iostwestcoast/Locker/Photos/photo_2022-11-24_02-31-49.jpg

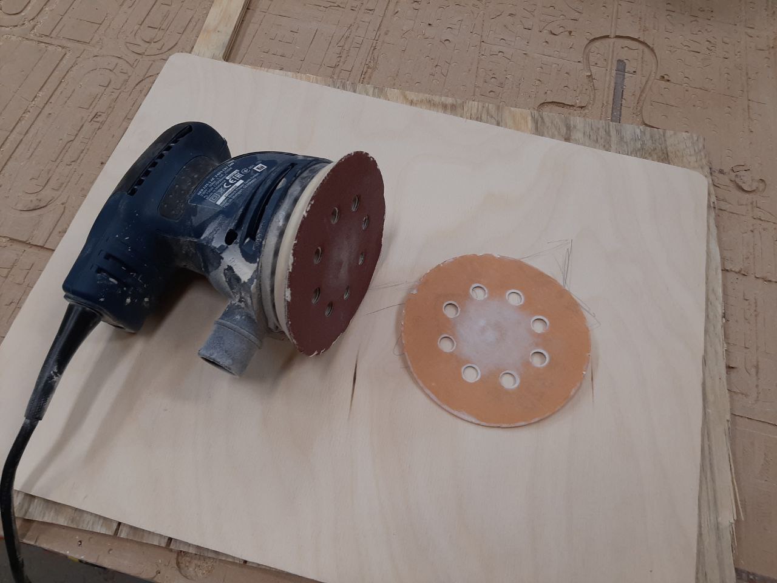
Photos/photo_2022-11-24_02-31-49.jpg
