iostwestcoast/Locker/Photos/photo_2022-11-24_02-31-54.jpg

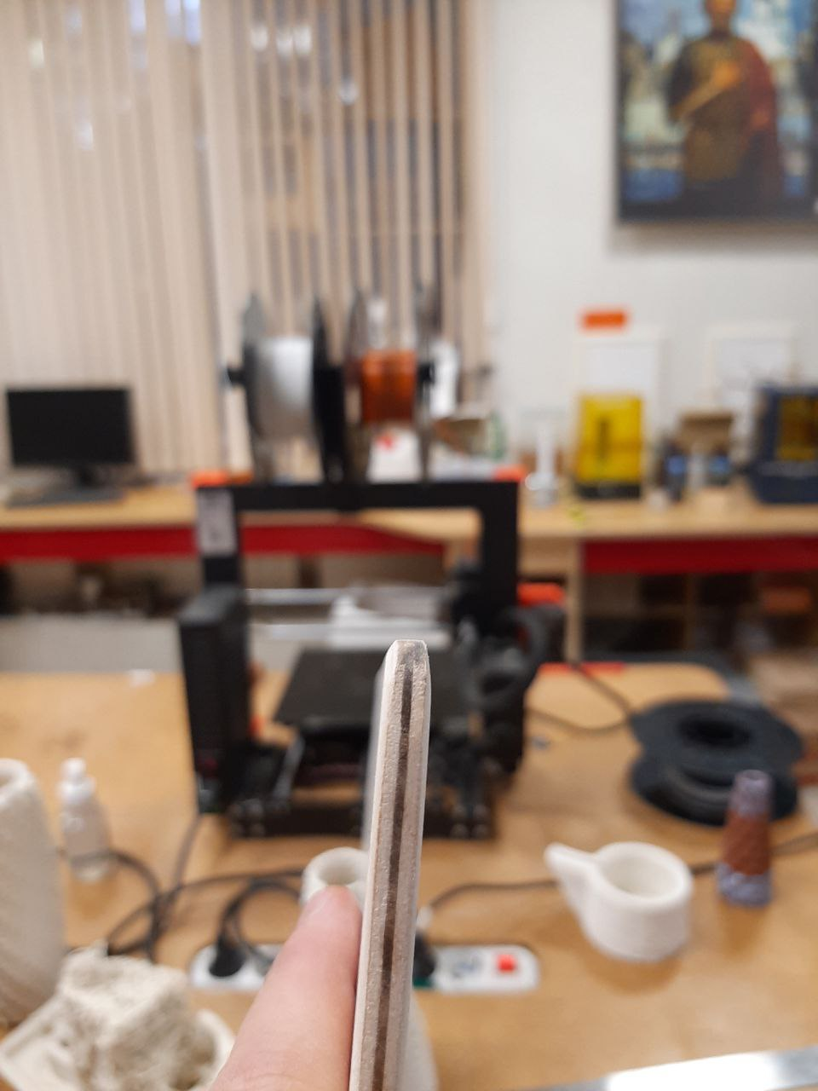
Photos/photo_2022-11-24_02-31-54.jpg
