iostwestcoast/Locker/Photos/photo_2022-11-24_02-32-23.jpg

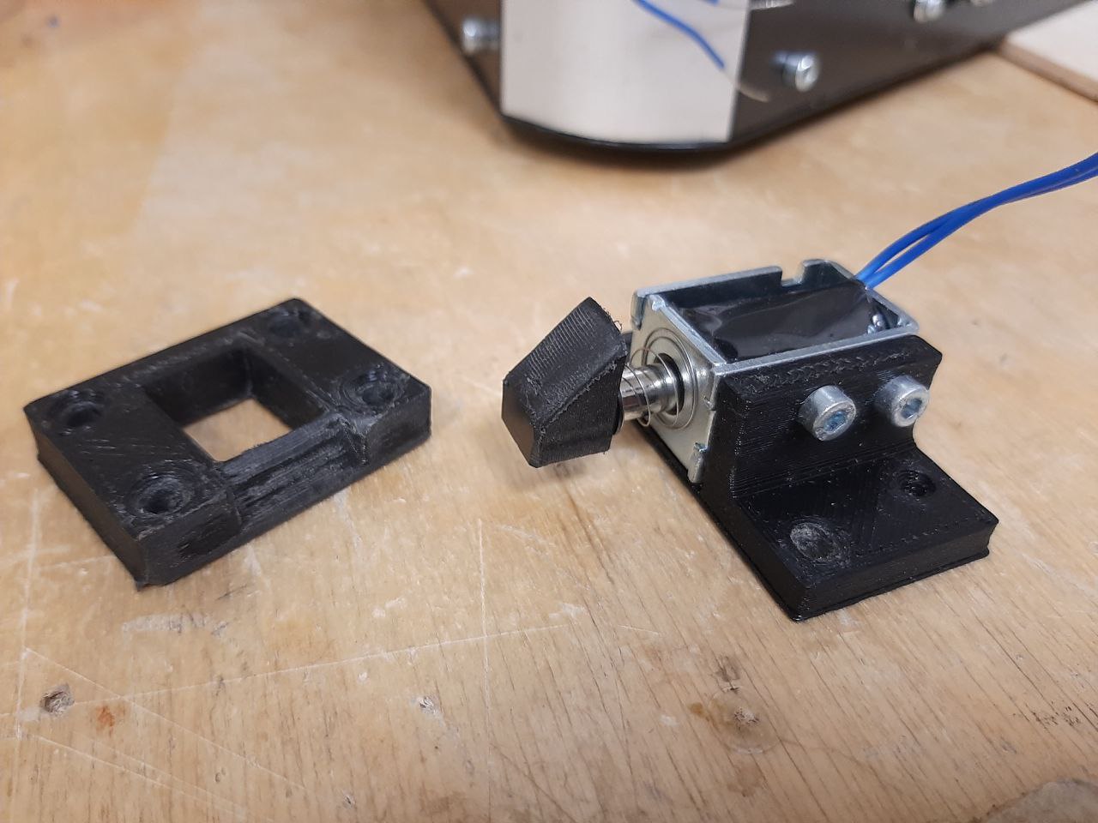
Photos/photo_2022-11-24_02-32-23.jpg
