iostwestcoast/Locker/Photos/photo_2022-11-24_02-32-27.jpg

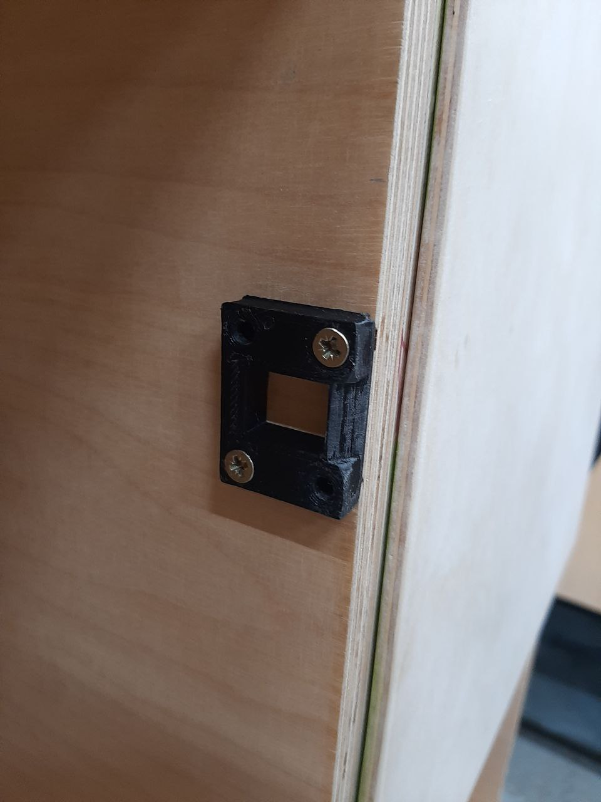
Photos/photo_2022-11-24_02-32-27.jpg
