iostwestcoast/Locker/Photos/photo_2022-11-24_02-32-28.jpg

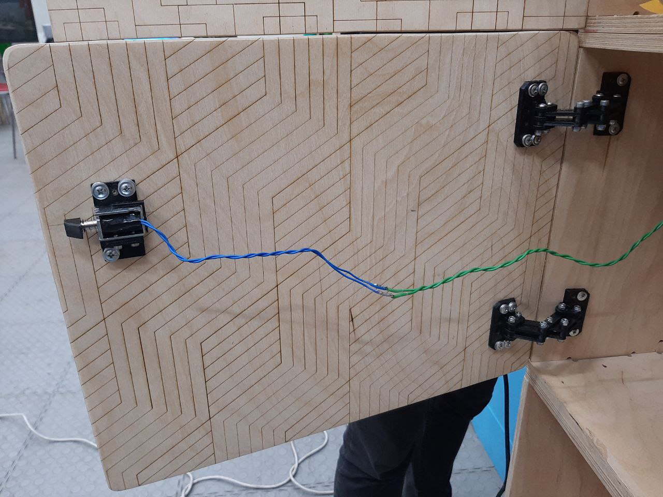
Photos/photo_2022-11-24_02-32-28.jpg
