iostwestcoast/Locker/Photos/photo_2022-11-24_02-32-32.jpg

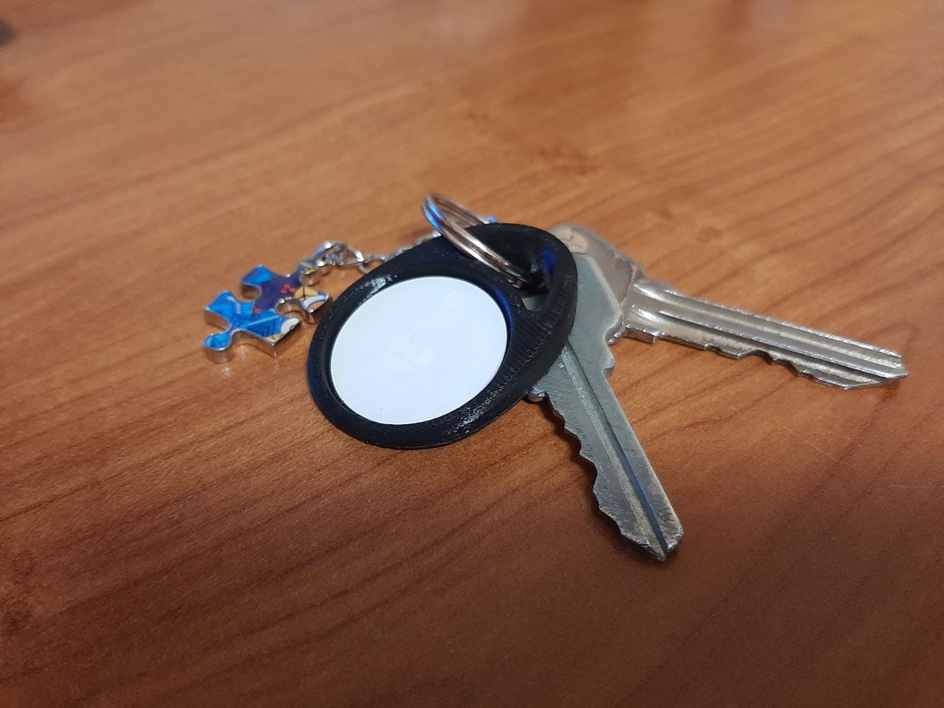
Photos/photo_2022-11-24_02-32-32.jpg
