iostwestcoast/Locker/Files/Bodykit on solenoid/solenoid_endstop.stl

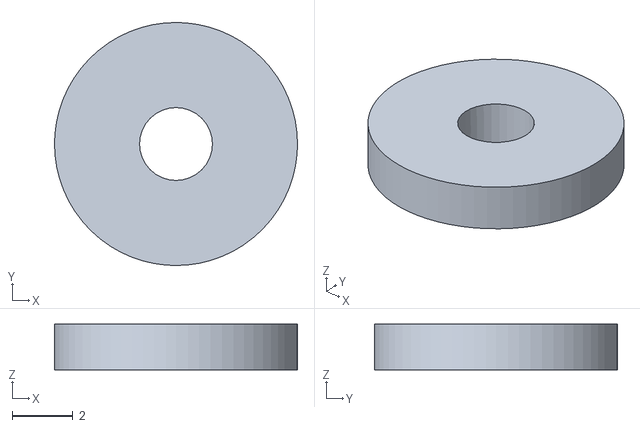
[picture p56: CAD file, 2022-11-24]
Files/Bodykit on solenoid/solenoid_endstop.stl
8.00 x 8.00 x 1.50
