iostwestcoast/Locker/Files/Door hinge assembly/Hinge_arm_-_long_6x.stl

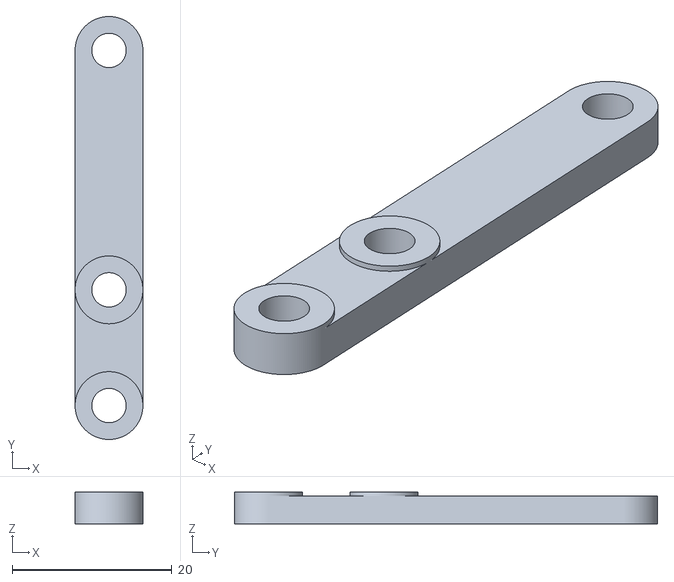
[picture p57: CAD file, 2022-11-24]
Files/Door hinge assembly/Hinge_arm_-_long_6x.stl
8.50 x 53.0 x 4.00
