iostwestcoast/Locker/Files/Door hinge/Base_Door_Side_v2.STL

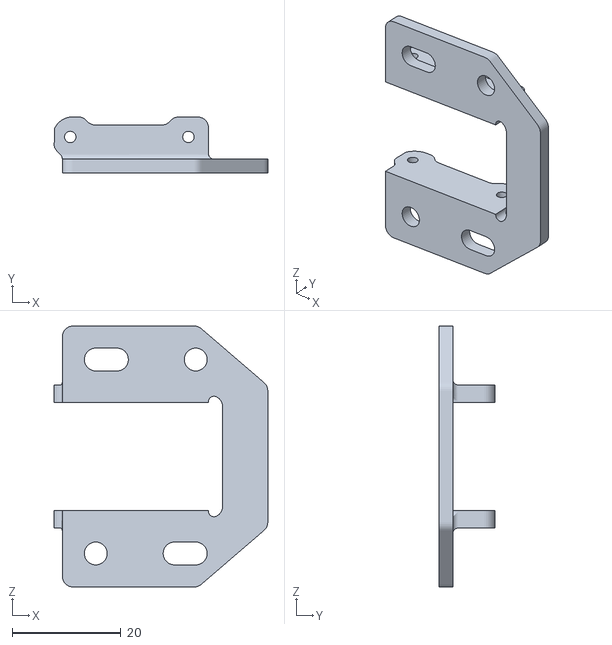
[picture p58: CAD file, 2022-11-24]
Files/Door hinge/Base_Door_Side_v2.STL
39.3 x 10.3 x 48.0
