iostwestcoast/Locker/Files/Rfid key fob/1/DD007.STL

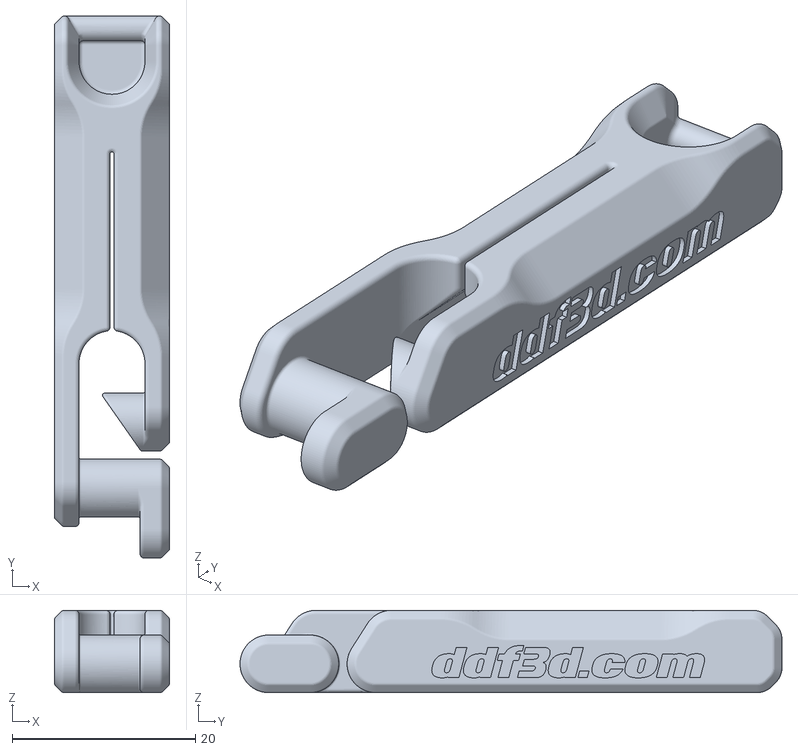
[picture p59: CAD file, 2022-11-24]
Files/Rfid key fob/1/DD007.STL
12.6 x 59.2 x 9.00
