iostwestcoast/Locker/Files/Rfid key fob/3/MILFALCON_2.stl

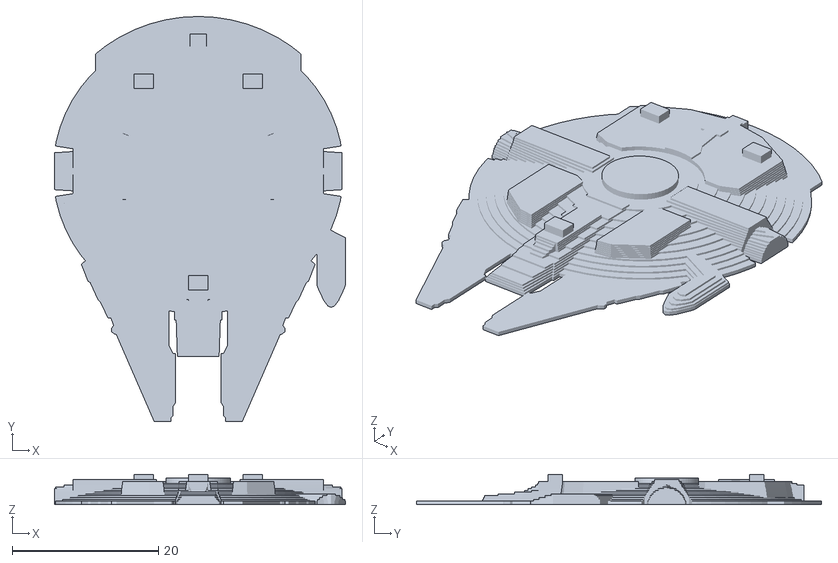
[picture p60: CAD file, 2022-11-24]
Files/Rfid key fob/3/MILFALCON_2.stl
39.8 x 55.4 x 4.12
