iostwestcoast/Locker/Files/Bodykit on solenoid/solenoid_holder.stl

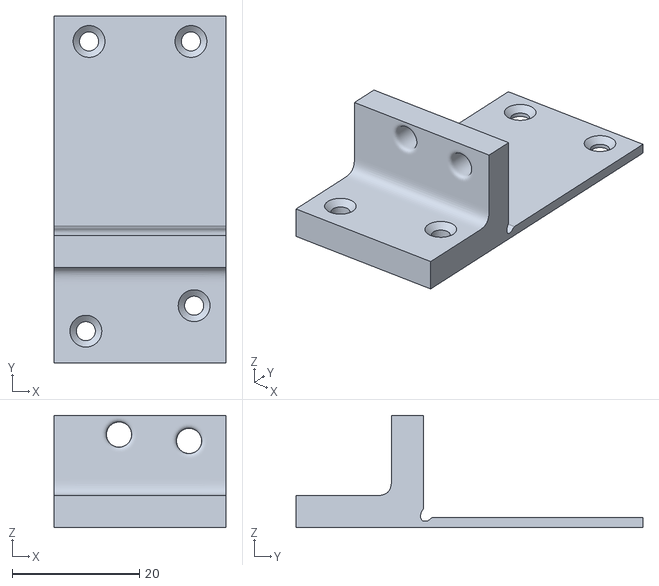
[picture p61: CAD file, 2022-11-24]
Files/Bodykit on solenoid/solenoid_holder.stl
27.0 x 54.5 x 17.6
