iostwestcoast/Locker/Files/Door hinge assembly/Hinge_arm_-_short_6x.stl

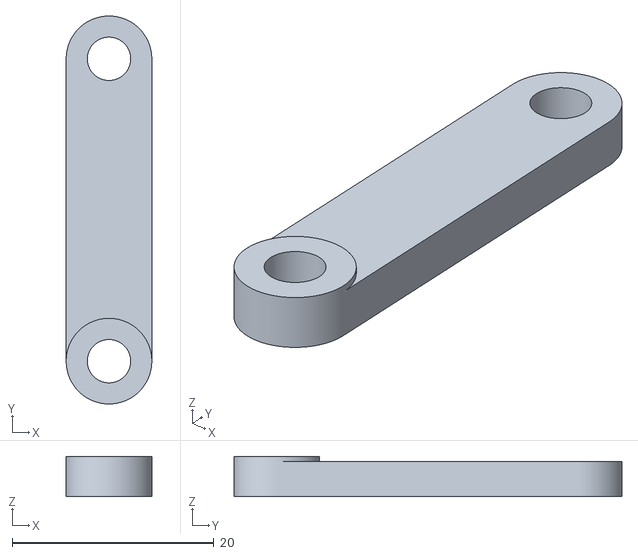
[picture p62: CAD file, 2022-11-24]
Files/Door hinge assembly/Hinge_arm_-_short_6x.stl
8.50 x 38.5 x 4.00
