iostwestcoast/Locker/Files/Door hinge/Articulating_Hinge_v2.3mf

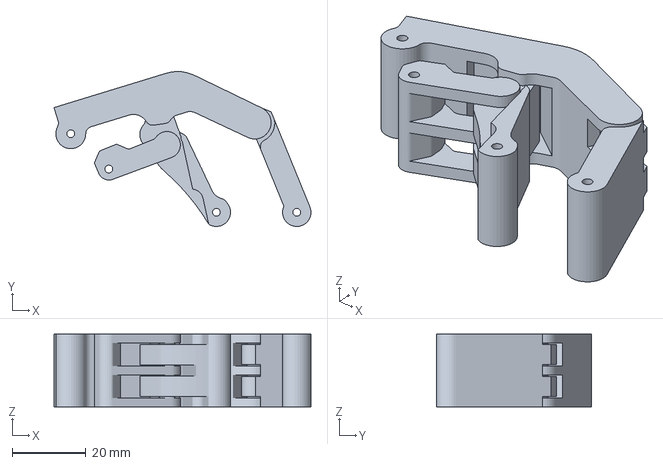
[picture p63: CAD file, 2022-11-24]
Files/Door hinge/Articulating_Hinge_v2.3mf
69.5 x 41.9 x 19.7 mm
