iostwestcoast/Locker/Files/Door hinge/SurfaceHinge.STEP

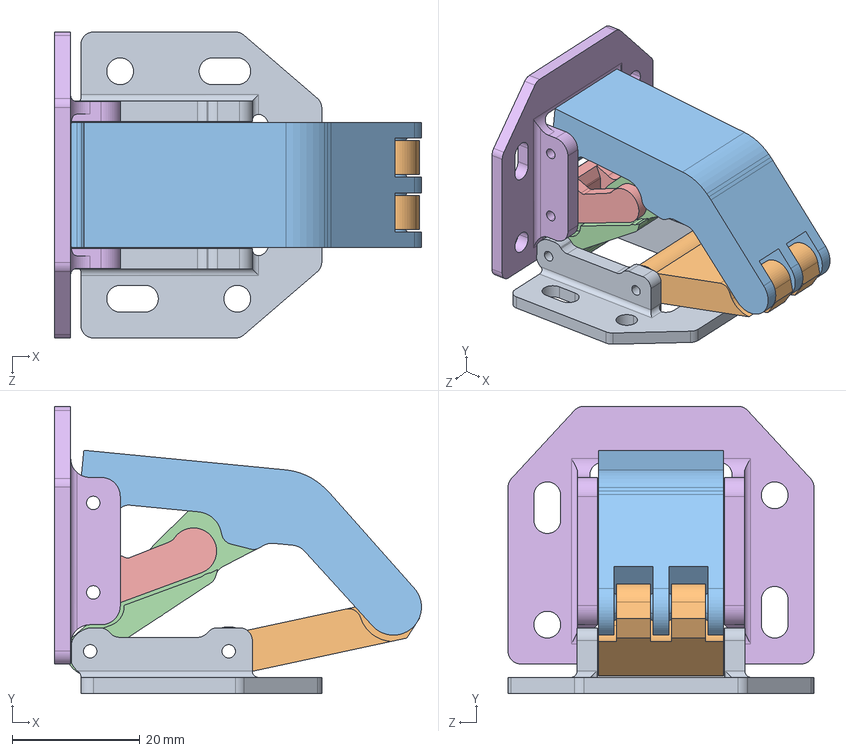
[picture p64: CAD file, 2022-11-24]
Files/Door hinge/SurfaceHinge.STEP
57.6 x 45.1 x 48.0 mm
Base_Door_Side_AK
Base_Frame_Side_AK
